bklemencz/8S001_PWM_485/FW/gamma.h

// Gamma brightness lookup table <https://victornpb.github.io/gamma-table-generator>
// gamma = 2.20 steps = 100 range = 0-1000
const uint16_t gamma_lut[100] = {
     0,   0,   0,   0,   1,   1,   2,   3,   4,   5,   6,   8,  10,  11,  14,  16,
    18,  21,  24,  26,  30,  33,  37,  40,  44,  48,  53,  57,  62,  67,  72,  78,
    83,  89,  95, 102, 108, 115, 122, 129, 136, 144, 152, 160, 168, 176, 185, 194,
   203, 213, 223, 232, 243, 253, 264, 274, 286, 297, 308, 320, 332, 345, 357, 370,
   383, 396, 410, 424, 438, 452, 466, 481, 496, 512, 527, 543, 559, 575, 592, 609,
   626, 643, 661, 679, 697, 715, 734, 753, 772, 791, 811, 831, 851, 871, 892, 913,
   935, 956, 978,1000,};
